landonr/homething-c6/case/model/keypad.py

"""The keys themselves: how big each one can be, the one continuous concave
recess sunk into the front face around them and around the wheel, and the soft
pad that carries a stem and a plunger under every switch.

The recess has two superellipse basins and one angular-blend wheel basin. Two
Hermite bridges make one C1 depth field, cut as one loft along y. Read
recess_spine() and face_depth_at() first: everything else about it, including
every check, is built off those two."""

import functools
import math
from collections import namedtuple

from build123d import (
    Box,
    BuildLine,
    BuildSketch,
    Cone,
    Face,
    Kind,
    Locations,
    Plane,
    Polyline,
    Pos,
    RectangleRounded,
    extrude,
    fillet,
    loft,
    make_face,
    offset,
)

import board
import cache
import params

from .hardware import legacy_screw_head, mount_points
from .legends import legend_solids
from .mic import mic_duct_or, mic_port
from .shape import (
    _cut,
    _fuse,
    _hole,
    _offset_face,
    _rounded_prism,
    _slab,
    _squircle_points,
    _squircle_prism,
)
from .stack import (
    CAP_BOTTOM,
    CAP_TOP,
    FDM_FACE,
    LEGACY_SWITCH_TOP,
    MERGE,
    PAD_SKIRT_BOTTOM,
    PAD_WEB_BOTTOM,
    PAD_WEB_TOP,
    SHELL_FRONT,
    STEM_TOP,
    STIFFENED_WALL,
    SWITCH_TOP,
    WHEEL_OPENING_R,
)
from .wheel_ring import (
    led_ring_roof_inner_r,
    led_ring_roof_outer_r,
    pad_clear_y,
)


def key_pitch():
    """Closest spacing of any two switches, which is what the keys have to fit in.

    Taken as the minimum rather than an average because the grid is not exact:
    SW4 sits 0.057 off its column and 0.026 off its row, so the tightest pair is
    12.42 where the nominal is 12.446.
    """
    parts = board.components()
    pts = [parts[ref][:2] for ref in board.refs("SW")]
    return min(
        math.dist(a, b) for i, a in enumerate(pts) for b in pts[i + 1 :]
    )


@functools.cache
def key_size(ref=None):
    """Side of the square key footprint at one switch, or the grid's own size
    for None.

    The grid pitch caps it, and a screw boss can cut it further: the collar
    has to stay outside the key hole, or the hole swallows the boss and
    leaves it hanging off the ceiling by nothing. All eleven take the full
    size now: SW1 and SW2 used to sit close enough to a pair of mounting
    holes to bind against this, back when there were four of them, but the
    board has moved to three and neither is close enough to shrink these
    two below the grid pitch any more. The clip stays, mechanical, in case
    a future layout brings a boss back into range.
    """
    limit = key_pitch() - params.KEY_GAP
    if ref is None:
        return limit
    x, y, _, _ = board.components()[ref]
    # Two circles, not one. The hole in the ceiling has to leave the boss its
    # collar, and the keytop has to stay out of the wider hole the pad needs where
    # the boss passes through it. The pad's is the larger and usually binds.
    collar = params.BOSS_OD / 2 + params.BOSS_COLLAR
    through = collar + params.PAD_BOSS_CLEARANCE

    def clears(size):
        for half, r in ((size / 2 + params.KEY_CLEARANCE, collar), (size / 2, through)):
            for hx, hy in mount_points():
                gap = math.hypot(max(abs(x - hx) - half, 0), max(abs(y - hy) - half, 0))
                if gap < r:
                    return False
        return True

    if clears(limit):
        return limit
    lo, hi = 0.0, limit
    for _ in range(40):
        mid = (lo + hi) / 2
        lo, hi = (mid, hi) if clears(mid) else (lo, mid)
    return lo


def island_refs(name):
    """The switches one keyed recess covers: KEYPAD_ISLAND_2 for "second",
    everything else for "grid". One reader, because the recess's own coverage
    box, the pad lobe under it and every per-key check have to agree on which
    keys belong where."""
    if name == "second":
        return [ref for ref in board.refs("SW") if ref in params.KEYPAD_ISLAND_2]
    return [ref for ref in board.refs("SW") if ref not in params.KEYPAD_ISLAND_2]


def key_recess(ref):
    """Which recess a switch sits in."""
    return "second" if ref in params.KEYPAD_ISLAND_2 else "grid"


def _key_bounds(refs):
    xs, ys = [], []
    parts = board.components()
    for ref in refs:
        x, y = parts[ref][:2]
        half = key_size(ref) / 2
        xs += [x - half, x + half]
        ys += [y - half, y + half]
    return xs, ys


def keypad_coverage():
    """[(name, x0, y0, x1, y1)] the plan footprint each keyed recess has to
    contain: the nine-key grid, and KEYPAD_ISLAND_2 (SW1, SW2) plus the mic
    inlet, each the bounding box of what it covers padded by KEYPAD_MARGIN on
    every side.

    Not the recess itself. keypad_recesses() grows a superellipse around each
    of these, because a superellipse only touches its own bounding box at the
    four edge midpoints and the corner keys sit nowhere near those.
    """
    out = []
    for name in ("grid", "second"):
        xs, ys = _key_bounds(island_refs(name))
        if name == "second":
            # KEYPAD_ISLAND_2's recess also covers the mic inlet, the other
            # aperture up at that end of the board.
            mx, my = mic_port()
            r = mic_duct_or()
            xs += [mx - r, mx + r]
            ys += [my - r, my + r]
        out.append(
            (
                name,
                min(xs) - params.KEYPAD_MARGIN,
                min(ys) - params.KEYPAD_MARGIN,
                max(xs) + params.KEYPAD_MARGIN,
                max(ys) + params.KEYPAD_MARGIN,
            )
        )
    return out


def exterior_x_bounds():
    """(x0, x1) of the case's own exterior side walls, the LAP_OUT profile's
    own extent. What KEYPAD_EDGE_MARGIN is measured from, and what
    EDGE_R_FRONT's fillet is cut from."""
    box = board.board_profile().bounding_box()
    over = params.BOARD_FIT + params.WALL
    return box.min.X - over, box.max.X + over


def exterior_y_bounds():
    """(y0, y1) of the case's own exterior end walls, the same profile the
    other way. The recesses are far clear of both ends, but the cap in
    keypad_recesses() is written for either axis so a layout change cannot
    quietly walk one off the end of the case."""
    box = board.board_profile().bounding_box()
    over = params.BOARD_FIT + params.WALL
    return box.min.Y - over, box.max.Y + over

@functools.cache
def centerline_x():
    """The x every recess is centred on and mirrored about.

    The three coverage centres and the wheel's own centre agree to a few
    hundredths on this board, which is what makes the whole recess a single
    column along y and so what makes one spine and one loft possible at all.
    They are averaged rather than one of them being picked, and check.py holds
    the spread, so a layout that pulled them apart would fail loudly instead of
    quietly shearing a dish sideways.
    """
    xs = [(x0 + x1) / 2 for _, x0, _, x1, _ in keypad_coverage()]
    xs.append(board.wheel_center()[0])
    return sum(xs) / len(xs)


def centerline_spread():
    """How far the furthest of those centres sits from centerline_x()."""
    xs = [(x0 + x1) / 2 for _, x0, _, x1, _ in keypad_coverage()]
    xs.append(board.wheel_center()[0])
    return max(abs(x - centerline_x()) for x in xs)


def _edge_room_x():
    """Half axis in x the exterior wall leaves, once KEYPAD_EDGE_MARGIN is taken
    off. Read at the centerline rather than at each recess's own centre, so
    both keyed dishes cap at the same half axis and the merged outline is
    symmetric about one line."""
    ex0, ex1 = exterior_x_bounds()
    cx = centerline_x()
    return min(cx - ex0, ex1 - cx) - params.KEYPAD_EDGE_MARGIN


def _edge_room_y(cy):
    """The same in y, for a dish centred there. Idle on this board, the recess
    running nowhere near either end wall, but written for either axis so a
    layout change cannot quietly walk one off the end of the case."""
    ey0, ey1 = exterior_y_bounds()
    return min(cy - ey0, ey1 - cy) - params.KEYPAD_EDGE_MARGIN


Recess = namedtuple("Recess", "name cy ax ay depth n")
"""One basin on the spine: where its centre sits along y, its two superellipse
half axes, how deep it is at that centre, and the exponent its own outline is
drawn with. All three share centerline_x()."""


@functools.cache
def keypad_recesses():
    """{name: Recess} for the three dishes the merged front-face recess is
    built from: the grid, the second island, and the wheel, in that order along
    y and disjoint in y.

    Each is a superellipse of exponent KEYPAD_SQUIRCLE_N about its own centre,
    with a depth that is zero on that curve and greatest at the centre. They
    are no longer separate cuts: keypad_necks() bridges them into one recess
    and recess_spine() is the merged field. What survives per dish is the
    outboard half of its rim, its own depth, and its own deepest point.

    The two keyed recesses are sized to *bound* their coverage box rather than
    to be inscribed in it. A superellipse inscribed in a box touches it only at
    the four edge midpoints and passes well inside the corners, which on this
    layout would put the rim straight through the four corner keys' own holes.
    Growing both half axes by 2^(1/n) is what puts the box's corners on the
    curve instead, and at n=4 that is about a fifth.

    Except in x on this board, where that reaches inside KEYPAD_EDGE_MARGIN.
    The x half axis is capped there and the y one is left alone rather than
    both being scaled back together: the cap costs dish beyond the coverage
    box's corners, and taking it out of one axis leaves more of the margin
    around the corner keys themselves than taking it out of both would.

    The wheel's is not sized off a coverage box at all. It has no keys under
    it, so its half axes are stated outright, WHEEL_BASIN_SPREAD past the bore on
    each axis and square, and what the bore does not swallow is the seat ring
    around the knob. WHEEL_RIM_LEDGE used to be that spread and is only the floor
    now: sizing the basin on the clearance minimum is what left the ring as
    narrow as the minimum. Its angular blend gives the cardinal axes circular
    curvature. WHEEL_SQUIRCLE_N keeps exact superellipse reach on the diagonals.

    That sizing rule still delivers WHEEL_RIM_LEDGE at every angle, and it does
    so for the same reason at either exponent. Above n=2 a superellipse's own
    axes are where it comes closest to its centre, so the half axis *is* the
    clearance, and the diagonals only ever stand further out. Below n=2 that
    inverts and the rule would stop holding, which is why check.py measures the
    clearance around the whole curve rather than trusting the arithmetic.
    """
    keyed = params.KEYPAD_SQUIRCLE_N
    grow = 2 ** (1 / keyed)
    room_x = _edge_room_x()
    out = {}
    for name, x0, y0, x1, y1 in keypad_coverage():
        cy = (y0 + y1) / 2
        depth = params.KEYPAD_DISH_DEPTH_2 if name == "second" else params.KEYPAD_DISH_DEPTH
        out[name] = Recess(
            name,
            cy,
            min((x1 - x0) / 2 * grow, room_x),
            min((y1 - y0) / 2 * grow, _edge_room_y(cy)),
            depth,
            keyed,
        )
    _, wy = board.wheel_center()
    half = WHEEL_OPENING_R + params.WHEEL_BASIN_SPREAD
    out["wheel"] = Recess(
        "wheel",
        wy,
        min(half, room_x),
        min(half, _edge_room_y(wy)),
        params.WHEEL_DISH_DEPTH,
        params.WHEEL_SQUIRCLE_N,
    )
    return {name: out[name] for name in sorted(out, key=lambda n: out[n].cy)}


def recess_span():
    """(y0, y1) the merged recess runs between: the outboard rim of the first
    dish to the outboard rim of the last."""
    dishes = list(keypad_recesses().values())
    return dishes[0].cy - dishes[0].ay, dishes[-1].cy + dishes[-1].ay


# The three spine quantities, per dish, on the centerline. Each is a plain
# function of y and each is what the merged field reduces to inside that dish's
# own body.
def _dish_shape(recess, y):
    """The cross-section shape parameter: the superellipse's own |dy/ay|^n.

    Zero on the basin's centre row, one at its rim. With the local exponent it
    is the only thing besides the local depth and the local half width that the
    cross-section depends on, which is what lets the merged field be exact
    inside a basin and still be built from four scalars per station."""
    return min(abs(y - recess.cy) / recess.ay, 1.0) ** recess.n


def _dish_width(recess, y):
    """Half width of one basin's plan outline at y."""
    if recess.name != "wheel":
        return recess.ax * max(0.0, 1.0 - _dish_shape(recess, y)) ** (1 / recess.n)

    v = min(abs(y - recess.cy) / recess.ay, 1.0)
    if v >= 1.0:
        return 0.0
    lo, hi = 0.0, 2 ** (0.5 - 1 / recess.n)
    for _ in range(52):
        mid = (lo + hi) / 2
        theta = math.atan2(v, mid)
        radius = _angular_radius(theta, recess.n, 1.0)
        if math.hypot(mid, v) < radius:
            lo = mid
        else:
            hi = mid
    return recess.ax * (lo + hi) / 2


def _dish_axis_rounding(recess, _y):
    """Amount of circular-axis angular blending in one basin."""
    return 1.0 if recess.name == "wheel" else 0.0


def _dish_edge_width(recess, y):
    """Plan half width at y, normalized by the basin's x half axis."""
    return _dish_width(recess, y) / recess.ax


def wheel_basin_width(y):
    """Half width of the unjoined wheel basin outline at y."""
    return _dish_width(keypad_recesses()["wheel"], y)


def _dish_depth(recess, y):
    """Depth on the centerline at y, which is the superellipse's own sag there:
    at dx=0 the exponent drops out and the profile is a plain circular arc in
    |dy/ay|."""
    u = min(abs(y - recess.cy) / recess.ay, 1.0)
    return recess.depth * math.sqrt(max(0.0, 1.0 - u * u))


SLOPE_STEP = 1e-6
"""Step the junction slopes are read off the dish functions with, by central
difference rather than by differentiating three functions by hand. At this step
the slope is right to about a part in a million, so the tangent break it leaves
at a junction is nine orders of magnitude under a print layer; check.py
measures the continuity rather than trusting it."""


def _slope(f, y):
    return (f(y + SLOPE_STEP) - f(y - SLOPE_STEP)) / (2 * SLOPE_STEP)


Neck = namedtuple("Neck", "name lower upper reach y0 y1")
"""One join between two basins: which two, how far into each it reaches (a pair,
lower then upper), and the two y stations the bridge runs between."""


@functools.cache
def keypad_necks():
    """[Neck] joining consecutive dishes along the spine, one per adjacent pair.

    A join starts each basin's own KEYPAD_JOIN_REACH inside that basin's rim, so
    the bridge has a finite slope to match at both ends and the two ends can be
    reached differently. Matching at the rims themselves is not possible: the
    sag's tangent there is vertical, and a bridge leaving a rim at a vertical
    tangent dives straight through zero.

    Where the bridge starts inside a basin, that basin's own inboard rim stops
    existing. That is the point of the merge, and it is why only the outboard
    halves of the outer two rims are still the superellipse. It is also what the
    reach buys: the further in it starts, the more width the outline has to turn
    through and the rounder the join reads.
    """
    dishes = list(keypad_recesses().values())
    out = []
    for lower, upper in zip(dishes, dishes[1:]):
        reaches = []
        for recess in (lower, upper):
            if recess.name not in params.KEYPAD_JOIN_REACH:
                raise ValueError(
                    f"no KEYPAD_JOIN_REACH entry for the {recess.name} basin: it "
                    "was renamed and how far a join may reach into it is unstated"
                )
            reaches.append(params.KEYPAD_JOIN_REACH[recess.name])
        out.append(
            Neck(
                f"{lower.name}-{upper.name}",
                lower,
                upper,
                tuple(reaches),
                lower.cy + lower.ay - reaches[0],
                upper.cy - upper.ay + reaches[1],
            )
        )
    return out


NECK_WAIST_SAMPLES = 400
"""How finely a join is walked to find its own waist and its own radius. Both
fall out of the bridge rather than being set, so both are measured."""


def neck_waist(neck):
    """(y, half_width, depth) at the narrowest point of one join.

    Measured, not set. The bridge is a single cubic from one dish's width to the
    other's, so where it is narrowest and how narrow that is are whatever the
    two ends and the reach leave.
    """
    span = neck.y1 - neck.y0
    best = None
    for i in range(NECK_WAIST_SAMPLES + 1):
        y = neck.y0 + span * i / NECK_WAIST_SAMPLES
        width = recess_spine(y)[0]
        if best is None or width < best[1]:
            best = (y, width, face_depth_at(centerline_x(), y))
    return best


def neck_radius(neck):
    """Tightest radius the plan outline turns through anywhere in one join.

    This is what "rounder" means and it is the number to read when changing a
    reach. The outline is x = centerline_x() +/- the spine's own width, so its
    curvature is the width function's, and a join that pinches shows up here as
    a small radius long before it shows up as a narrow waist: the waist width
    barely moved when the old two-cubic bridge was dropped, and this roughly
    tripled.
    """
    span = neck.y1 - neck.y0
    step = span / NECK_WAIST_SAMPLES
    tightest = float("inf")
    for i in range(2, NECK_WAIST_SAMPLES - 1):
        y = neck.y0 + span * i / NECK_WAIST_SAMPLES
        first = (recess_spine(y + step)[0] - recess_spine(y - step)[0]) / (2 * step)
        second = (
            recess_spine(y + step)[0]
            - 2 * recess_spine(y)[0]
            + recess_spine(y - step)[0]
        ) / step**2
        if abs(second) > 1e-12:
            tightest = min(tightest, (1 + first * first) ** 1.5 / abs(second))
    return tightest


def _hermite(t, p0, m0, p1, m1, span):
    """Cubic Hermite on [0, 1], with the end slopes given per unit y and the
    interval's own length so they can be."""
    return (
        (2 * t**3 - 3 * t**2 + 1) * p0
        + (t**3 - 2 * t**2 + t) * span * m0
        + (-2 * t**3 + 3 * t**2) * p1
        + (t**3 - t**2) * span * m1
    )


def recess_spine(y):
    """(half_width, depth, shape, exponent, axis_rounding, edge_width) at y:
    everything the cross-section at that station needs.

    Inside a dish's body all six are that dish's own functions. Inside a neck,
    all six are Hermite bridges that match value and slope at both ends. This
    makes the merged field C1 across a junction rather than only continuous.

    All six get one cubic across the whole join, so nothing has a waypoint of
    its own: the floor simply ramps from one basin surface to the other and the
    outline simply turns from one rim into the other. Width used to get two
    cubics instead, meeting at the join's midpoint at a stated waist with zero
    slope, and that flat spot is what made the joins read as tight pinches: a
    single cubic at the same reach turns through roughly three times the radius.
    What the waist comes out as is now measured (neck_waist()) and bounded from
    below (KEYPAD_NECK_MIN) rather than set.

    The exponent is bridged as well, the wheel's basin carrying its own. It is
    constant inside a basin, so its bridge leaves either end with zero slope and
    the cross-section morphs from one basin's curve to the other's without a
    tangent break of its own.

    Joins are tested first because their intervals deliberately reach inside the
    dishes they bridge.
    """
    for neck in keypad_necks():
        if neck.y0 <= y <= neck.y1:
            lower, upper = neck.lower, neck.upper
            span = neck.y1 - neck.y0
            t = (y - neck.y0) / span
            depth = _hermite(
                t,
                _dish_depth(lower, neck.y0),
                _slope(lambda v: _dish_depth(lower, v), neck.y0),
                _dish_depth(upper, neck.y1),
                _slope(lambda v: _dish_depth(upper, v), neck.y1),
                span,
            )
            shape = _hermite(
                t,
                _dish_shape(lower, neck.y0),
                _slope(lambda v: _dish_shape(lower, v), neck.y0),
                _dish_shape(upper, neck.y1),
                _slope(lambda v: _dish_shape(upper, v), neck.y1),
                span,
            )
            width = _hermite(
                t,
                _dish_width(lower, neck.y0),
                _slope(lambda v: _dish_width(lower, v), neck.y0),
                _dish_width(upper, neck.y1),
                _slope(lambda v: _dish_width(upper, v), neck.y1),
                span,
            )
            exponent = _hermite(t, lower.n, 0.0, upper.n, 0.0, span)
            axis_rounding = _hermite(
                t,
                _dish_axis_rounding(lower, neck.y0),
                0.0,
                _dish_axis_rounding(upper, neck.y1),
                0.0,
                span,
            )
            edge_width = _hermite(
                t,
                _dish_edge_width(lower, neck.y0),
                _slope(lambda v: _dish_edge_width(lower, v), neck.y0),
                _dish_edge_width(upper, neck.y1),
                _slope(lambda v: _dish_edge_width(upper, v), neck.y1),
                span,
            )
            return (
                max(width, 0.0),
                max(depth, 0.0),
                min(max(shape, 0.0), 1.0),
                max(exponent, 2.0),
                min(max(axis_rounding, 0.0), 1.0),
                max(edge_width, 0.0),
            )
    for recess in keypad_recesses().values():
        if abs(y - recess.cy) <= recess.ay:
            return (
                _dish_width(recess, y),
                _dish_depth(recess, y),
                _dish_shape(recess, y),
                recess.n,
                _dish_axis_rounding(recess, y),
                _dish_edge_width(recess, y),
            )
    return 0.0, 0.0, 1.0, params.KEYPAD_SQUIRCLE_N, 0.0, 0.0


SHAPE_LIMIT = 1e-9
"""How close the shape parameter may come to one before _cross() switches to
its own limit. At one the normalised profile is 0/0, and the limit it tends to
is the superellipse's own outline exponent."""


def _angular_radius(theta, n, axis_rounding):
    """Normalized radius of the angular circle-to-superellipse blend."""
    c, s = abs(math.cos(theta)), abs(math.sin(theta))
    squircle = (c**n + s**n) ** (-1 / n)
    weight = axis_rounding * (1.0 - math.sin(2 * theta) ** 2)
    return squircle + weight * (1.0 - squircle)


def _cross(u, shape, n, axis_rounding=0.0, edge_width=0.0):
    """The cross-section profile across x, normalised to one on the centerline
    and zero at the rim: u is |dx| over the local half width.

    This is the superellipse's own section rather than a shape of its own,
    which is what makes the merged field exactly the basin's own field inside a
    basin body. Substituting the local half width into
    |dx/ax|^n + |dy/ay|^n = s^n leaves s^n = shape + u^n (1 - shape), so the
    whole section is fixed by the shape parameter and the exponent, and dividing
    by its own value at u=0 leaves this.
    """
    if u >= 1.0:
        return 0.0
    if axis_rounding > 0.0 and edge_width > 0.0:
        x = u * edge_width
        y = shape ** (1 / n)
        theta = math.atan2(y, x)
        rho = math.hypot(x, y) / _angular_radius(theta, n, axis_rounding)
        edge_theta = math.atan2(y, edge_width)
        edge_rho = math.hypot(edge_width, y) / _angular_radius(
            edge_theta, n, axis_rounding
        )
        span = edge_rho * edge_rho - y * y
        if span <= 0.0:
            return 0.0
        return math.sqrt(max(0.0, edge_rho * edge_rho - rho * rho) / span)
    if 1.0 - shape < SHAPE_LIMIT:
        return math.sqrt(max(0.0, 1.0 - u**n))
    top = 1.0 - (shape + u**n * (1.0 - shape)) ** (2 / n)
    bottom = 1.0 - shape ** (2 / n)
    return math.sqrt(max(0.0, top / bottom))


def face_depth_at(x, y):
    """How far below SHELL_FRONT the merged recess's floor sits at (x, y), zero
    outside its rim.

    The one piece of recess arithmetic in the model. The loft is built from it,
    check.py measures the built solid against it, and mic.py opens the inlet at
    whatever it says the floor is over the board's acoustic port, so none of
    the three can drift from the others.
    """
    width, depth, shape, n, axis_rounding, edge_width = recess_spine(y)
    if width <= 0.0 or depth <= 0.0:
        return 0.0
    return depth * _cross(
        abs(x - centerline_x()) / width,
        shape,
        n,
        axis_rounding,
        edge_width,
    )


def face_floor_at(x, y):
    """The z of that floor."""
    return SHELL_FRONT - face_depth_at(x, y)


DEPTH_OVER_SAMPLES = 400
"""How finely face_depth_over() walks y across a footprint. The x half of that
search is exact, so this is the whole resolution of it; over a counterbore's
own width it puts the samples a few thousandths apart."""


def face_depth_over(x, y, half):
    """Deepest the recess gets anywhere over an axis-aligned square of side
    2*half centred at (x, y).

    Exact in x, sampled in y. The profile falls off monotonically with |dx|, so
    at any y the deepest x over the square is whichever of the centerline or
    the nearer edge lies in it, which is a clamp. Along y the spine has three
    humps and two necks and is not monotone anywhere useful, so that half is
    walked rather than solved.
    """
    xs = min(max(centerline_x(), x - half), x + half)
    return max(
        face_depth_at(xs, y - half + 2 * half * i / DEPTH_OVER_SAMPLES)
        for i in range(DEPTH_OVER_SAMPLES + 1)
    )


def face_plan_margin(x, y, half, samples=None):
    """Least recess left in plan between a keycap counterbore of side 2*half
    centred at (x, y) and the merged rim, measured across the recess.

    The counterbore is a superellipse of KEY_SQUIRCLE_N, the cap chain's own
    exponent, so it is sampled as one rather than as the rounded square it used
    to be. That tightens the reading rather than loosening it: a superellipse
    pulls in from a rounded square's corner, so the hole's outermost point is
    nearer the centre than it was. The exponent is the caps' rather than the
    rim's because it is a cap-chain width being measured; the two were one
    number until the caps got their flanks bowed out.

    What a key hole actually has to satisfy. KEYPAD_MARGIN is stated on the
    coverage box's own edges, and the superellipse bounding that box reaches
    further than the box on the axes and less far at the corners, so the margin
    a corner key really gets is neither of those numbers and has to be
    measured. The rim is x = centerline_x() +/- recess_spine()'s own width, so
    the distance to it across the recess is that width less the point's own
    offset; negative means the rim runs through the hole, and a point past
    either end of the spine reads negative because the width there is zero.
    """
    cx = centerline_x()
    count = params.KEY_SQUIRCLE_POINTS if samples is None else samples
    outline = _squircle_points(x, y, half, half, params.KEY_SQUIRCLE_N, count)
    return min(recess_spine(py)[0] - abs(px - cx) for px, py in outline)


RING_ROOF_ANGLES = 180
RING_ROOF_RADII = 21
"""How the ring roof's own annulus is walked. Both axes, not just the inner
radius: the rotary dish is concentric with the channel and so is deepest over
it at that inner edge, but the grid's and the second island's rims cross the
same annulus from outside and get deeper the further out they reach, so a
single radius answers for one of the three and not the others."""


def ring_roof_left():
    """Thinnest translucent roof left over the LED ring channel, face side.

    LED_RING_ROOF is what the roof would be under a flat face. Three things
    dish the face over the channel: the wheel basin reaching past its own
    half axis on the diagonals, and both necks running out across the annulus
    on the way to the dishes either side. What any of them sinks there comes
    out of this.

    The annulus walked is the roof's own, inner wall to outer. The inner wall
    is plumb, so that end is simply led_ring_inner_r() and the walk runs nearer
    the bore than it did when the wall raked away from it, which is where the
    wheel basin is deepest.
    """
    wx, wy = board.wheel_center()
    lo, hi = led_ring_roof_inner_r(), led_ring_roof_outer_r()
    deepest = 0.0
    for i in range(RING_ROOF_ANGLES):
        a = 2 * math.pi * i / RING_ROOF_ANGLES
        for j in range(RING_ROOF_RADII):
            r = lo + (hi - lo) * j / (RING_ROOF_RADII - 1)
            deepest = max(
                deepest, face_depth_at(wx + r * math.cos(a), wy + r * math.sin(a))
            )
    return params.LED_RING_ROOF - deepest


LEDGE_SAMPLES = 2000
"""Points the merged rim is walked at when measuring its clearance from the
wheel opening's bore. Dense because the closest approach is on the wheel
basin's own flanks, where the rim runs nearly parallel to the bore and the
minimum is shallow in y."""


def wheel_ledge_left():
    """Closest the merged rim comes to the wheel opening's bore, radially.

    Measured on the built spine rather than on the wheel basin's own formula,
    so it answers for the joins as well: their bridges take over the outline
    either side of the basin and are free to run somewhere the formula says
    nothing about. Negative would mean the rim crossing into the bore, which
    would put a step in the seat instead of a dished ring.

    It used to read a hundredth under WHEEL_RIM_LEDGE, the basin having been
    sized on exactly that clearance; WHEEL_BASIN_SPREAD sizes it now and this
    stands well clear. The hundredth is still there and TOLERANCE still absorbs
    it: the basin is centred on the shared centreline while the bore is centred
    on the wheel's own centre, and centerline_x() averages the two apart by that
    much.
    """
    cx = centerline_x()
    wx, wy = board.wheel_center()
    y0, y1 = recess_span()
    best = float("inf")
    for i in range(LEDGE_SAMPLES + 1):
        y = y0 + (y1 - y0) * i / LEDGE_SAMPLES
        width = recess_spine(y)[0]
        if width <= 0:
            continue
        for x in (cx - width, cx + width):
            best = min(best, math.hypot(x - wx, y - wy) - WHEEL_OPENING_R)
    return best


def recess_stations():
    """The y values the merged recess is lofted through, sorted.

    Per dish, stations at the superellipse's own parameter rather than at even
    steps in y: both the half width and the depth turn fastest at a rim and
    barely at all in the middle, and even steps in the parameter put the
    stations where the turning is. The outermost is KEYPAD_TIP_WIDTH of a half
    axis wide rather than a point, since a degenerate section is what makes a
    loft come back non-manifold; the superellipse's own end is flat to within
    microns over that width, so the blunt tip it leaves is faithful rather than
    a compromise.

    Plus even steps across each neck, where nothing is singular and the two
    Hermite halves want resolving on their own terms rather than on the
    neighbouring dish's.
    """
    count = params.KEYPAD_RECESS_STATIONS
    ys = set()
    for recess in keypad_recesses().values():
        n = recess.n
        offsets = [
            recess.ay * math.sin((math.pi / 2) * k / count) ** (2 / n)
            for k in range(count)
        ]
        offsets.append(recess.ay * (1 - params.KEYPAD_TIP_WIDTH**n) ** (1 / n))
        for dy in offsets:
            ys.add(round(recess.cy + dy, 9))
            ys.add(round(recess.cy - dy, 9))
    for neck in keypad_necks():
        steps = params.KEYPAD_NECK_STATIONS
        for i in range(steps + 1):
            ys.add(round(neck.y0 + (neck.y1 - neck.y0) * i / steps, 9))
    return sorted(ys)


SECTION_MIN_WIDTH = 0.01
"""Floor under a station's own half width, so one landing exactly on a rim
still makes a closed wire rather than a line and the loft has something to work
with. recess_stations() keeps every station KEYPAD_TIP_WIDTH of a half axis
clear of a rim, so this never fires on the present layout; it is here so that a
future station list cannot turn a loft into a crash."""


def _station_section(y):
    """The merged recess's cross-section at one station, as a face in that
    station's own plane: the floor curve under the recess, carried up the two
    vertical rim walls and closed across MERGE above the face.

    Wound counter-clockwise in (x, z) deliberately. BuildSketch mirrors a
    clockwise sketch about the workplane's own axis, so the sag would come back
    above the face instead of below it.

    The floor's points are spaced by angle across the section rather than
    evenly in x, for the same reason the stations are: the profile stands
    vertical where it meets a rim, and even steps in x leave the last chord
    cutting the corner off.
    """
    width, depth, shape, n, axis_rounding, edge_width = recess_spine(y)
    width = max(width, SECTION_MIN_WIDTH)
    cx = centerline_x()
    count = params.KEYPAD_PROFILE_POINTS
    points = []
    for i in range(count + 1):
        u = math.sin(-math.pi / 2 + math.pi * i / count)
        points.append(
            (
                cx + u * width,
                SHELL_FRONT
                - depth * _cross(abs(u), shape, n, axis_rounding, edge_width),
            )
        )
    points.append((cx + width, SHELL_FRONT + MERGE))
    points.append((cx - width, SHELL_FRONT + MERGE))
    plane = Plane.XZ.offset(-y)
    with BuildSketch(plane) as sketch:
        with BuildLine(plane):
            Polyline(*points, close=True)
        make_face()
    return sketch.sketch.faces()[0]


@cache.solid
def keypad_recess():
    """The whole front-face recess as the one solid the shell cuts: a smooth
    loft along y through recess_stations()' cross-sections.

    One cut, not five. The three basins and the two joins are one C1 depth
    field (recess_spine()), and the region it covers is a single column along
    y, one interval in x per station, so a loft along that column reproduces
    the field with a single wall surface and no seam in it anywhere. Fusing
    five lofts would have left a tangent-continuous surface with four edges
    across it, and the merge exists precisely so there are none.

    ruled=True, and it has to be. A fitted loft is the obvious choice on a
    surface whose whole point is that it has no creases, and it worked until the
    wheel basin took its own exponent: fitting a spline in y through this many
    sections is unstable, and the parameter change was enough to tip it over
    into diverging outright, returning a solid of negative volume spread over
    half a metre. The stations are what carry the fidelity in y instead, and
    they carry it easily. They are spaced by the superellipse's own parameter,
    so the chord between two of them departs from the field by well under a
    micron anywhere, which is three orders under a print layer and two under
    what check.py's own probes straddle. The other axis is a polyline already
    (KEYPAD_PROFILE_POINTS), so this makes the surface a fine polygonal
    approximation in both directions rather than one, which is the honest
    description of what it always was.

    Every station carries the same point count regardless, so the loft has a
    vertex to match at each and nothing to guess.

    backform.py gave up a fitted loft for the same underlying reason, where it
    overshot its sections rather than diverging. Treat one through many sections
    as suspect in this model.
    """
    return loft([_station_section(y) for y in recess_stations()], ruled=True)


def recess_outline():
    """The merged recess's plan outline, as one closed face in the z=0 plane.

    Built from the same half widths the loft's own sections are, read at the
    same recess_stations(), so the line the FDM front draws in its face is the
    rim the recessed front has there and not an approximation of it. Up the
    right-hand side and back down the left: the field is one interval in x per
    station by construction, which is what makes the outline a single closed
    polygon rather than several loops.

    Nothing clamps it. The rim runs inside EDGE_R_FRONT, so an outline drawn on
    a front with that round would spend most of its length on the round's
    curve; on the FDM front a smaller chamfer leaves flat face for it.
    Clamping the outline was the other way round and it
    showed: it flat-sided the line over most of its length and carried it into
    the LED ring channel.
    """
    cx = centerline_x()
    ys = recess_stations()
    points = [(cx + recess_spine(y)[0], y) for y in ys]
    points += [(cx - recess_spine(y)[0], y) for y in reversed(ys)]
    with BuildSketch(Plane.XY) as sketch:
        with BuildLine(Plane.XY):
            Polyline(*points, close=True)
        make_face()
    return sketch.sketch.faces()[0]


@cache.solid
def keypad_outline_groove():
    """The FDM front's face marking: recess_outline() as a shallow slot.

    A true 2D offset either side of the outline rather than the outline's own
    half width moved in x. The two differ wherever the outline turns away from
    the y axis, which is both tips and the outboard flank of every rim, and
    moving x there leaves the slot wider than it was asked for and closes it to
    a filled blob at the tips, where the outline's own width falls under the
    offset. Kind.ARC rounds the outside of a convex turn, which is what a
    constant-width slot around a closed curve is.

    Cut to FDM_OUTLINE_DEPTH and carried MERGE past the face, so the cut
    breaks through the plane rather than leaving a skin of it behind.
    """
    face = recess_outline()
    band = offset(
        face, amount=params.FDM_OUTLINE_W / 2, kind=Kind.ARC
    ) - offset(face, amount=-params.FDM_OUTLINE_W / 2, kind=Kind.ARC)
    groove = extrude(band, amount=params.FDM_OUTLINE_DEPTH + MERGE)
    return Pos(0, 0, FDM_FACE - params.FDM_OUTLINE_DEPTH) * groove


def outline_length():
    """Length of the outline's own centreline, for a pass that wants the mean
    width the built groove came out as rather than the one it was asked for."""
    return recess_outline().outer_wire().length


def keypad_recess_facts():
    """What the merged recess came out as: one entry per dish and one per neck,
    plus how close the whole thing comes to the exterior wall.

    Shared by case.py's summary print and check.py's guards, so both read the
    same numbers rather than each re-deriving them.
    """
    ex0, ex1 = exterior_x_bounds()
    cx = centerline_x()
    out = {"dishes": {}, "necks": {}}
    for name, recess in keypad_recesses().items():
        depths = [
            face_depth_at(*board.components()[ref][:2]) for ref in island_refs(name)
        ] if name != "wheel" else []
        out["dishes"][name] = {
            "center": (cx, recess.cy),
            "half": (recess.ax, recess.ay),
            "depth": recess.depth,
            "n": recess.n,
            "key_depths": (min(depths), max(depths)) if depths else None,
        }
    for neck in keypad_necks():
        span = neck.y1 - neck.y0
        floor = min(
            face_depth_at(cx, neck.y0 + span * i / NECK_WAIST_SAMPLES)
            for i in range(NECK_WAIST_SAMPLES + 1)
        )
        waist_y, waist_half, waist_depth = neck_waist(neck)
        out["necks"][neck.name] = {
            "reach": neck.reach,
            "span": (neck.y0, neck.y1),
            "waist": (waist_y, waist_half, waist_depth),
            "radius": neck_radius(neck),
            "floor": floor,
            "ends": (_dish_width(neck.lower, neck.y0), _dish_width(neck.upper, neck.y1)),
        }
    widest = max(r.ax for r in keypad_recesses().values())
    out["edge_gap"] = min(cx - widest - ex0, ex1 - cx - widest)
    out["centerline"] = (cx, centerline_spread())
    out["stations"] = len(recess_stations())
    return out


def centerline_keys_span():
    """(y0, y1) between the outermost key rows of the two keyed islands: the
    grid's own top row's far edge and the second island's bottom row's far
    edge, each taken at the counterbore rather than the switch centre.

    What the recess has to stay open across, which is what check.py's neck
    continuity pass measures. Not the neck's own span: a neck that pinched
    apart would still be a neck, and what would be lost is the recess running
    unbroken from one island's keys to the other's.
    """
    parts = board.components()
    grid = max(parts[ref][1] for ref in island_refs("grid"))
    second = min(parts[ref][1] for ref in island_refs("second"))
    return grid + key_size() / 2, second - key_size() / 2


def pad_lobes():
    """[(name, x0, y0, x1, y1)] one rectangle per keypad island: that island's
    own keys, padded PAD_MARGIN on every side.

    The keys alone. The mic is not in it, unlike the recess above: the pad is
    there to carry stems and plungers, and the inlet's duct comes down outside
    it.
    """
    out = []
    for name in ("grid", "second"):
        xs, ys = _key_bounds(island_refs(name))
        out.append(
            (
                name,
                min(xs) - params.PAD_MARGIN,
                min(ys) - params.PAD_MARGIN,
                max(xs) + params.PAD_MARGIN,
                max(ys) + params.PAD_MARGIN,
            )
        )
    return out


def pad_wheel_gap():
    """Closest either lobe comes to the pad's own wheel clearance band,
    pad_clear_y() either side of the wheel centre.

    The band used to be a cut: the pad was one full-width slab and the bore
    severed it. The lobes are tight rectangles now and stop short of the band
    on their own, so there is nothing left to cut and this is the number that
    says so. It is what keeps the lip's rotating clearance and the LEDs' own
    sight line free of silicone, which is what the band was for.
    """
    _, wy = board.wheel_center()
    half = pad_clear_y()
    return min(
        min(abs(y0 - wy), abs(y1 - wy)) - half for _, _, y0, _, y1 in pad_lobes()
    )


def _pad_limit():
    """The stiffened wall, inset by PAD_FIT: what each lobe is clipped inside.

    Active on both lobes, whose key rectangles reach past it at the long
    sides. Taken off STIFFENED_WALL everywhere, so the plain IR end keeps a
    wider gap than PAD_FIT."""
    wall = _offset_face(STIFFENED_WALL)
    return Face(wall.outer_wire().offset_2d(-params.PAD_FIT, kind=Kind.INTERSECTION))


def pad_bridge_top():
    """Place the lower bridge below each boss clearance between the buttons."""
    parts = board.components()
    refs = sorted(island_refs("second"), key=lambda ref: parts[ref][0])
    left = parts[refs[0]][0] + key_size(refs[0]) / 2 + params.PAD_MARGIN
    right = parts[refs[-1]][0] - key_size(refs[-1]) / 2 - params.PAD_MARGIN
    top = min(parts[ref][1] for ref in refs)
    radius = params.BOSS_OD / 2 + params.BOSS_COLLAR + params.PAD_BOSS_CLEARANCE
    for x, y in mount_points():
        if left < x < right:
            top = min(top, y - radius - params.PAD_BOSS_CLEARANCE)
    return top


def pad_lobe_face(name):
    """Round each button contour near the mic and keep the lower web attached."""
    x0, y0, x1, y1 = next(box[1:] for box in pad_lobes() if box[0] == name)
    with BuildSketch() as sketch:
        with Locations(((x0 + x1) / 2, (y0 + y1) / 2)):
            RectangleRounded(x1 - x0, y1 - y0, params.PAD_RADIUS)
    rect = sketch.sketch.faces()[0]
    outline = extrude(rect, amount=1, dir=(0, 0, 1))
    if name == "second":
        parts = board.components()
        refs = island_refs(name)
        bridge_top = pad_bridge_top()
        lower = outline.intersect(
            Pos((x0 + x1) / 2, (y0 + bridge_top) / 2, 0.5)
            * Box(x1 - x0 + 2, bridge_top - y0, 1)
        ).solids()[0]
        keys = []
        for ref in refs:
            x, y = parts[ref][:2]
            size = key_size(ref) + 2 * params.PAD_MARGIN
            keys.append(_rounded_prism(x, y, size, params.PAD_RADIUS, 0, 1))
            keys.append(
                Pos(x, (bridge_top - MERGE + y) / 2, 0.5)
                * Box(size, y - bridge_top + MERGE, 1)
            )
        contour = _fuse(lower, *keys).faces().sort_by()[0]
        joins = [
            vertex for vertex in contour.vertices()
            if abs(vertex.Y - bridge_top) < 1e-6
            and x0 + params.PAD_RADIUS < vertex.X < x1 - params.PAD_RADIUS
        ]
        contour = contour.fillet_2d(params.PAD_JOIN_RADIUS, joins)
        outline = extrude(contour, amount=1, dir=(0, 0, 1)).intersect(outline).solids()[0]
    clipped = outline & extrude(
        _pad_limit(), amount=1, dir=(0, 0, 1)
    )
    return clipped.faces().sort_by()[0]


def _grid_axes(axis):
    """Ordered grid row or column coordinates, read from SW3 through SW11.

    SW4 and SW7 are slightly off their nominal column or row. Group positions
    within 0.1 mm so each physical grid line still produces one coordinate.
    """
    index = 0 if axis == "x" else 1
    values = sorted(board.components()[ref][index] for ref in island_refs("grid"))
    groups = []
    for value in values:
        if not groups or value - groups[-1][-1] > 0.1:
            groups.append([value])
        else:
            groups[-1].append(value)
    if len(groups) != 3:
        raise ValueError(f"nine-button grid has {len(groups)} {axis} lines, not three")
    return [sum(group) / len(group) for group in groups]


def _pad_groove_specs():
    """FDM isolation-groove plan data derived from the nine switch coordinates.

    Each tuple is (orientation, centre, run0, run1). A vertical groove runs
    along Y between adjacent switch columns. A horizontal groove runs along X
    between adjacent switch rows. Only the grid lobe appears here.
    """
    _, x0, y0, x1, y1 = next(box for box in pad_lobes() if box[0] == "grid")
    columns = _grid_axes("x")
    rows = _grid_axes("y")
    edge = -params.FDM_PAD_GROOVE_EDGE_OVERTRAVEL
    return tuple(
        ("vertical", (a + b) / 2, y0 + edge, y1 - edge)
        for a, b in zip(columns, columns[1:])
    ) + tuple(
        ("horizontal", (a + b) / 2, x0 + edge, x1 - edge)
        for a, b in zip(rows, rows[1:])
    )


def _pad_grooves():
    """Rounded flat-bottom FDM cuts for each grid centreline, from the keytop face only.

    The plunger face stays flat for supports.
    """
    width = params.FDM_PAD_GROOVE_W
    depth = params.FDM_PAD_GROOVE_DEPTH
    if width <= 0 or depth <= 0:
        raise ValueError("pad groove width and depth must be positive")
    if depth >= params.PAD_WEB_T:
        raise ValueError("FDM pad groove depth leaves no web")
    chamfer = params.FDM_PAD_GRID_CHAMFER
    if not 0 < chamfer <= depth:
        raise ValueError("FDM pad groove chamfer must be positive and at most the groove depth")
    cuts = []
    for orientation, centre, run0, run1 in _pad_groove_specs():
        length = run1 - run0
        if length <= width:
            raise ValueError("pad groove edge treatment leaves no groove run")
        x, y = ((centre, (run0 + run1) / 2) if orientation == "vertical"
                else ((run0 + run1) / 2, centre))
        size_x, size_y = ((width, length) if orientation == "vertical"
                          else (length, width))
        with BuildSketch() as sketch:
            with Locations((x, y)):
                # build123d requires a radius strictly below half the narrow
                # dimension. One micron preserves the intended semicircle.
                RectangleRounded(size_x, size_y, width / 2 - 0.001)
        face = sketch.sketch.faces()[0]
        cut = _slab(face, PAD_WEB_TOP - depth, PAD_WEB_TOP + MERGE)
        # Negative taper grows the slot 1 mm per 1 mm of height (45 degrees).
        flare = extrude(Pos(0, 0, PAD_WEB_TOP - chamfer) * face,
                        amount=chamfer + MERGE, taper=-45)
        cuts.append(_fuse(cut, flare))
    return cuts


def _stem(x, y):
    """The soft stem a cap sits over, raised out of the pad where a keytop was.

    Square rather than round, because the legend on the cap has an orientation
    and a round stem holds none. It starts inside the web rather than on it, so
    it merges into one solid, and it reaches the socket ceiling, so a press
    drives through the stem rather than through the flange.

    A plain prism, no barb. The flange retains the cap now, and a barb would put
    an undercut on every stem in a moulded pad while fighting the blind assembly
    that seats nine of them at once.
    """
    return _rounded_prism(x, y, params.STEM_W, params.STEM_R, PAD_WEB_BOTTOM, STEM_TOP)


def fdm_cap_body(ref):
    """Side of an integrated FDM keytop."""
    flange = key_size(ref) - 2 * params.CAP_FLANGE_TRIM
    face_hole = flange - 2 * params.CAP_FLANGE_OVERLAP
    return face_hole - 2 * params.FDM_CAP_GUIDE_CLEARANCE


def fdm_keycap_bottom():
    """Bottom of each integrated FDM keytop, flush with its lobe web."""
    return PAD_WEB_TOP


def fdm_keycap(ref, legend=True):
    """One solid keytop for the FDM pad, fused across its lobe web.

    It keeps the normal cap's visible superellipse, exposed-top fillet, and
    debossed legend, but it has no flange or socket. Its bottom is flush with
    the web, which removes the cap-to-stem step. The keytops stop short of the
    grid grooves, so each button still has independent flex. `legend=False`
    leaves the top blank for geometry checks.
    """
    x, y = board.components()[ref][:2]
    body = _squircle_prism(
        x,
        y,
        fdm_cap_body(ref),
        params.KEY_SQUIRCLE_N,
        params.KEY_SQUIRCLE_POINTS,
        fdm_keycap_bottom(),
        CAP_TOP,
    )
    top_edges = [
        edge
        for edge in body.edges()
        if edge.bounding_box().min.Z > CAP_TOP - 0.01
    ]
    if not top_edges:
        raise ValueError(f"{ref}'s FDM keytop has no top perimeter edges to fillet")
    body = fillet(top_edges, params.CAP_TOP_FILLET)
    marks = legend_solids(ref, x, y) if legend else []
    return _cut(body, *marks)


def _boss_clearances(x0, y0, x1, y1):
    """The holes a lobe needs where a front-plate boss passes through it.

    Off the boss's collar, not the boss, so a stem clears the ceiling the collar
    leaves behind as well as the boss itself. A boss whose clearance circle
    crosses the lobe's edge would leave a crescent bite ending in two cusps
    there, so that cut gains a slot out through the edge and becomes an open U
    instead: same rounded end, straight sides, no points. All four edges are
    tested now that a lobe is a tight rectangle rather than the full cavity
    width.
    """
    clearance_d = params.BOSS_OD + 2 * (params.BOSS_COLLAR + params.PAD_BOSS_CLEARANCE)
    r = clearance_d / 2
    bottom, top = PAD_SKIRT_BOTTOM - 1, STEM_TOP + 1
    out = []
    for x, y in mount_points():
        if x < x0 - r or x > x1 + r or y < y0 - r or y > y1 + r:
            continue
        cut = _hole(x, y, clearance_d, bottom, top)
        for edge, axis, out_dir in (
            (x0, "x", -1),
            (x1, "x", 1),
            (y0, "y", -1),
            (y1, "y", 1),
        ):
            here = x if axis == "x" else y
            if abs(here - edge) >= r:
                continue
            reach = abs(here - edge) + 1
            dx = out_dir * reach / 2 if axis == "x" else 0
            dy = out_dir * reach / 2 if axis == "y" else 0
            size = (reach, clearance_d) if axis == "x" else (clearance_d, reach)
            cut = _fuse(
                cut,
                Pos(x + dx, y + dy, (bottom + top) / 2)
                * Box(size[0], size[1], top - bottom),
            )
        out.append(cut)
    return out


def _mic_clearance():
    """Open-edge clearance around the mic duct's widest ceiling chamfer."""
    x, y = mic_port()
    diameter = 2 * (
        mic_duct_or() + params.STANDOFF_CHAMFER + params.PAD_MIC_CLEARANCE
    )
    return _hole(x, y, diameter, PAD_SKIRT_BOTTOM - 1, PAD_WEB_TOP + 1)


def plunger(x, y, contact=SWITCH_TOP, extension=params.PLUNGER_SWITCH_EXTENSION):
    """Build one plunger with a 45 degree lower-edge chamfer and flat contact.

    `contact` is the switch top it engages and `extension` how far it reaches
    below it. The V2 top pad's nibs pass LEGACY_SWITCH_TOP and
    LEGACY_NIB_EXTENSION, so they engage a V2 switch by a shorter extension.
    """
    z0 = contact - extension
    size = params.PLUNGER_LOWER_CHAMFER
    radius = params.PLUNGER_D / 2
    if size <= 0 or size >= radius or size >= PAD_WEB_TOP - z0:
        raise ValueError("plunger lower chamfer must leave a flat contact and upper shaft")
    contact_radius = radius - size
    chamfer = Pos(x, y, z0 + size / 2) * Cone(
        bottom_radius=contact_radius,
        top_radius=radius,
        height=size,
    )
    shaft = _hole(x, y, params.PLUNGER_D, z0 + size, PAD_WEB_TOP)
    return _fuse(chamfer, shaft)


@functools.cache
def _skirt_ring(name, bottom=PAD_SKIRT_BOTTOM):
    """The moulded skirt before any break: lobe outline less its PAD_SKIRT_T inset."""
    face = pad_lobe_face(name)
    inner = Face(face.outer_wire().offset_2d(-params.PAD_SKIRT_T, kind=Kind.ARC))
    return _cut(
        _slab(face, bottom, PAD_WEB_BOTTOM + MERGE),
        _slab(inner, bottom - 1, PAD_WEB_BOTTOM + MERGE + 1),
    )


@functools.cache
def _v3_skirt_obstacles():
    """[(ref, solid)] every V3 assembly solid under the V3 placement nearest it."""
    return [
        (ref, solid)
        for ref, solids in sorted(board.placement_groups().items())
        for solid in solids
    ]


def _skirt_breaks(name, obstacles, bottom):
    """[(ref, box)] cuts that open a skirt of the given `bottom` over each of
    `obstacles`, a list of (ref, solid)."""
    clear = params.PAD_SKIRT_CLEARANCE
    ring = _skirt_ring(name, bottom)
    ring_box = ring.bounding_box()
    groups = {}
    for ref, solid in obstacles:
        box = solid.bounding_box()
        if box.max.Z <= bottom - clear:
            continue
        if (box.max.X + clear < ring_box.min.X or box.min.X - clear > ring_box.max.X
                or box.max.Y + clear < ring_box.min.Y or box.min.Y - clear > ring_box.max.Y):
            continue
        reach = Pos((box.min.X + box.max.X) / 2, (box.min.Y + box.max.Y) / 2, 0) * Box(
            box.max.X - box.min.X + 2 * clear,
            box.max.Y - box.min.Y + 2 * clear,
            100,
        )
        hit = ring.intersect(reach)
        if hit is None or not hit.solids():
            continue
        groups.setdefault(ref, []).append(box)
    z0, z1 = bottom - 1, PAD_WEB_BOTTOM + MERGE + 1
    out = []
    for ref in sorted(groups):
        boxes = groups[ref]
        lo_x = min(b.min.X for b in boxes) - clear
        hi_x = max(b.max.X for b in boxes) + clear
        lo_y = min(b.min.Y for b in boxes) - clear
        hi_y = max(b.max.Y for b in boxes) + clear
        out.append((ref, Pos((lo_x + hi_x) / 2, (lo_y + hi_y) / 2, (z0 + z1) / 2)
                    * Box(hi_x - lo_x, hi_y - lo_y, z1 - z0)))
    return out


def pad_skirt_breaks(name):
    """[(ref, box)] cuts that open the skirt over each board part it would touch.

    A part counts if its top is above PAD_SKIRT_BOTTOM less PAD_SKIRT_CLEARANCE
    and its plan box, grown by PAD_SKIRT_CLEARANCE, reaches the skirt. One box
    per nearest placement, over all of that part's solids.
    """
    return _skirt_breaks(name, _v3_skirt_obstacles(), PAD_SKIRT_BOTTOM)


def pad_skirt(name):
    """The moulded lobe's skirt: a PAD_SKIRT_T wall flush with the lobe outline.

    It drops from the web to PAD_SKIRT_BOTTOM, level with the plungers, and is
    cut open over each board part before it fuses to the web. The moulded and
    TPU pads share it.
    """
    return _cut(_skirt_ring(name), *(box for _, box in pad_skirt_breaks(name)))


LEGACY_SKIRT_NAME = "V2_RETENTION_HOLE"
"""Name of the V2 skirt break over the retention screw head."""


@functools.cache
def legacy_skirt_obstacles():
    """[(ref, solid)] what the V2 top pad's skirt must clear, in the case frame
    with the V2 board in place: the V3 body of each V2 top-side part moved to
    its V2 placement and dropped SUPPORT_GAP, and the V2 screw head.

    Every V2 part on the top side that has a V3 body is moved. The break rule
    then keeps only those that reach the second lobe's skirt.
    """
    legacy = board.legacy_components()
    out = []
    for ref in sorted(board.placement_groups()):
        if ref not in legacy or legacy[ref][3] != "top":
            continue
        for solid in board.legacy_part_solids(ref):
            out.append((ref, Pos(0, 0, -params.SUPPORT_GAP) * solid))
    out.append((LEGACY_SKIRT_NAME, legacy_screw_head()))
    return out


def legacy_pad_skirt():
    """The second lobe's skirt for the V2 top pad: bottom level with the V3
    pad's skirt (PAD_SKIRT_BOTTOM), broken over the V2 obstacles."""
    return _cut(
        _skirt_ring("second", PAD_SKIRT_BOTTOM),
        *(box for _, box in legacy_skirt_breaks()),
    )


def legacy_skirt_breaks():
    """[(name, box)] the V2 top pad's skirt breaks, by the same rule as
    pad_skirt_breaks over legacy_skirt_obstacles()."""
    return _skirt_breaks("second", legacy_skirt_obstacles(), PAD_SKIRT_BOTTOM)


@cache.solid
def button_pad(fdm=False, skirt=None, grooves=True, legend=True, v2=False):
    """Build two pad lobes supported by their switch plungers.

    The mic lobe follows both buttons with a connected lower bridge.
    Both lobes stop outside the wheel clearance band. With fdm=True, the
    printed keytops and legends are fused to their lobe webs in this export.
    `skirt` adds the perimeter skirt and defaults to the moulded pad only.
    `grooves` applies only when `fdm` is true; False gives the FDM pad a plain grid web with no grooves and no edge chamfer.
    `legend` False leaves every printed keytop blank. `v2` swaps the second lobe for `legacy_top_pad`, so one part fits a V2 board.
    """
    return _fuse(
        *(
            legacy_top_pad(skirt=bool(skirt), fdm=fdm, legend=legend)
            if v2 and name == "second"
            else _pad_lobe(name, fdm, skirt=skirt, grooves=grooves, legend=legend)
            for name, *_ in pad_lobes()
        )
    )


def _pad_lobe(
    name,
    fdm,
    nibs=(),
    plunger_extension=params.PLUNGER_SWITCH_EXTENSION,
    skirt=None,
    grooves=True,
    skirt_part=None,
    legend=True,
):
    """Build one pad lobe. Each (x, y) in `nibs` adds a plunger to a V2 switch.

    `skirt` None means a skirt only when `fdm` is false. `skirt_part` replaces
    the lobe's own skirt solid. `plunger_extension` is how far each of the lobe's own
    plungers reaches below SWITCH_TOP. `grooves` applies only when `fdm` is true.
    `legend` False leaves the printed keytops blank.
    """
    parts = board.components()
    x0, y0, x1, y1 = next(box[1:] for box in pad_lobes() if box[0] == name)
    body = _slab(pad_lobe_face(name), PAD_WEB_BOTTOM, PAD_WEB_TOP)
    skirt = not fdm if skirt is None else skirt
    if fdm and grooves and name == "grid":
        c = params.FDM_PAD_GRID_CHAMFER
        face = pad_lobe_face(name)
        body = _fuse(
            _slab(face, PAD_WEB_BOTTOM, PAD_WEB_TOP - c),
            # The lobe face points -Z, so the taper needs an explicit +Z.
            extrude(Pos(0, 0, PAD_WEB_TOP - c) * face, amount=c, dir=(0, 0, 1), taper=45),
        )
    if skirt:
        body = _fuse(body, pad_skirt(name) if skirt_part is None else skirt_part)
    raised = []
    for ref in island_refs(name):
        x, y = parts[ref][:2]
        raised.append(_stem(x, y))
        raised.append(plunger(x, y, extension=plunger_extension))
        if fdm:
            raised.append(fdm_keycap(ref, legend=legend))
    raised.extend(
        plunger(x, y, LEGACY_SWITCH_TOP, params.LEGACY_NIB_EXTENSION)
        for x, y in nibs
    )
    cuts = _boss_clearances(x0, y0, x1, y1)
    if name == "second":
        cuts.append(_mic_clearance())
    elif fdm and grooves:
        cuts.extend(_pad_grooves())
    return _cut(_fuse(body, *raised), *cuts)


@cache.solid
def legacy_top_pad(skirt=False, fdm=True, legend=True):
    """Build the pad's SW1/SW2 lobe for a V2 board only.

    It keeps the V3 plungers and adds one nib at each V2 switch, which sits
    further -Y and lower, on the retention post. Nibs and kept plungers both
    extend LEGACY_NIB_EXTENSION below their own switch top, so the plungers
    stay SUPPORT_GAP above the nibs.
    `skirt` adds the one-piece TPU pad's skirt, ending level with the V3 pad's
    skirt (PAD_SKIRT_BOTTOM) and broken over the V2 parts and the V2 screw head. With `fdm` false the lobe is the
    moulded pad's: plain web, stems for the separate caps, no fused keytops.
    `legend` False leaves the fused keytops blank.
    """
    legacy = board.legacy_components()
    nibs = [legacy[ref][:2] for ref in island_refs("second")]
    return _pad_lobe(
        "second",
        fdm=fdm,
        nibs=nibs,
        plunger_extension=params.LEGACY_NIB_EXTENSION,
        skirt=skirt,
        skirt_part=legacy_pad_skirt() if skirt else None,
        legend=legend,
    )
